ylu12358/mae-148-sp24-team4/CAD/GPS/GPS Antenna.SLDPRT

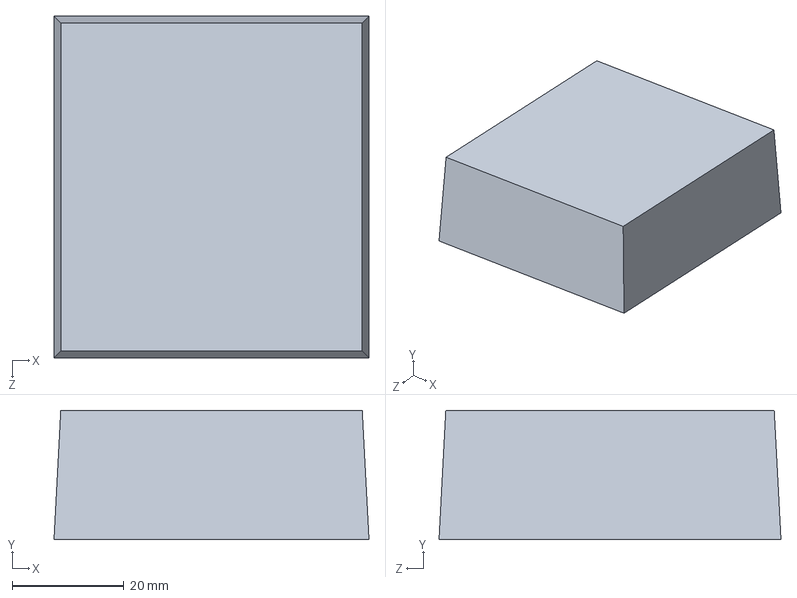
[picture p22: CAD file, 2024-04-26]
CAD/GPS/GPS Antenna.SLDPRT
56.5 x 23.1 x 61.3 mm
