ylu12358/mae-148-sp24-team4/CAD/Jetson/NanoMeshMini-Bottom-Jetson-Nano-DevKit-Case.stl

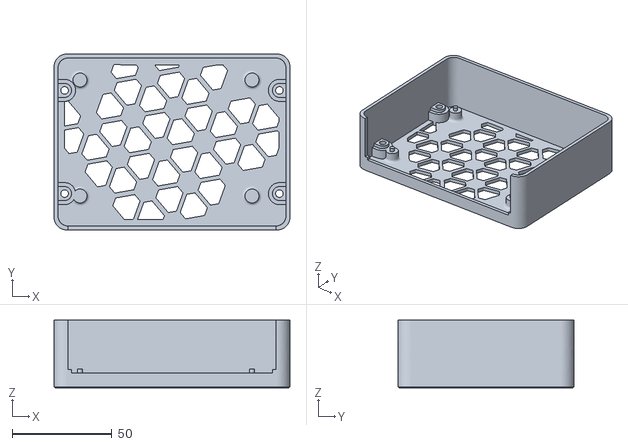
[picture p23: CAD file, 2024-04-19]
CAD/Jetson/NanoMeshMini-Bottom-Jetson-Nano-DevKit-Case.stl
118.0 x 88.0 x 34.0
