ylu12358/mae-148-sp24-team4/CAD/LIDAR/LIDAR Mount.SLDPRT

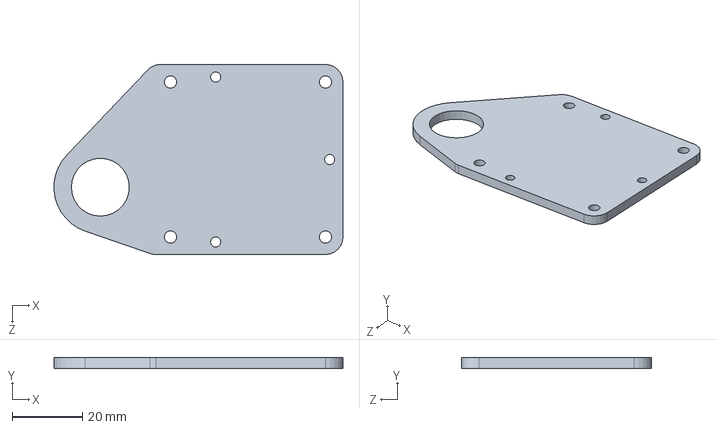
[picture p24: CAD file, 2024-04-28]
CAD/LIDAR/LIDAR Mount.SLDPRT
82.4 x 3.00 x 54.2 mm
