ylu12358/mae-148-sp24-team4/CAD/VESC.SLDPRT

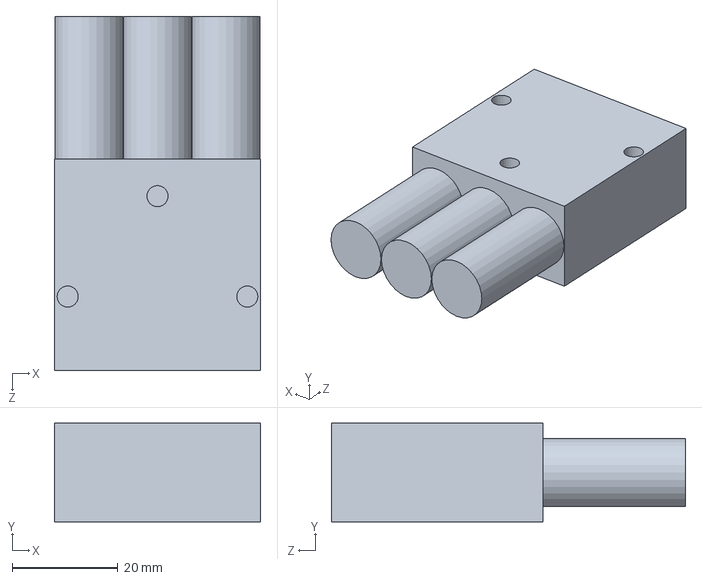
[picture p25: CAD file, 2024-04-19]
CAD/VESC.SLDPRT
39.0 x 18.7 x 67.0 mm
