ylu12358/mae-148-sp24-team4/CAD/Anti Spark Switch.SLDPRT

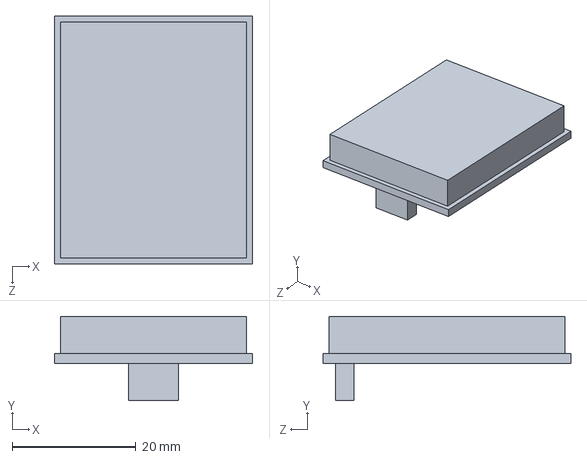
[picture p26: CAD file, 2024-04-19]
CAD/Anti Spark Switch.SLDPRT
32.0 x 13.6 x 40.0 mm
