ylu12358/mae-148-sp24-team4/CAD/Camera/Camera Mount Base.SLDPRT

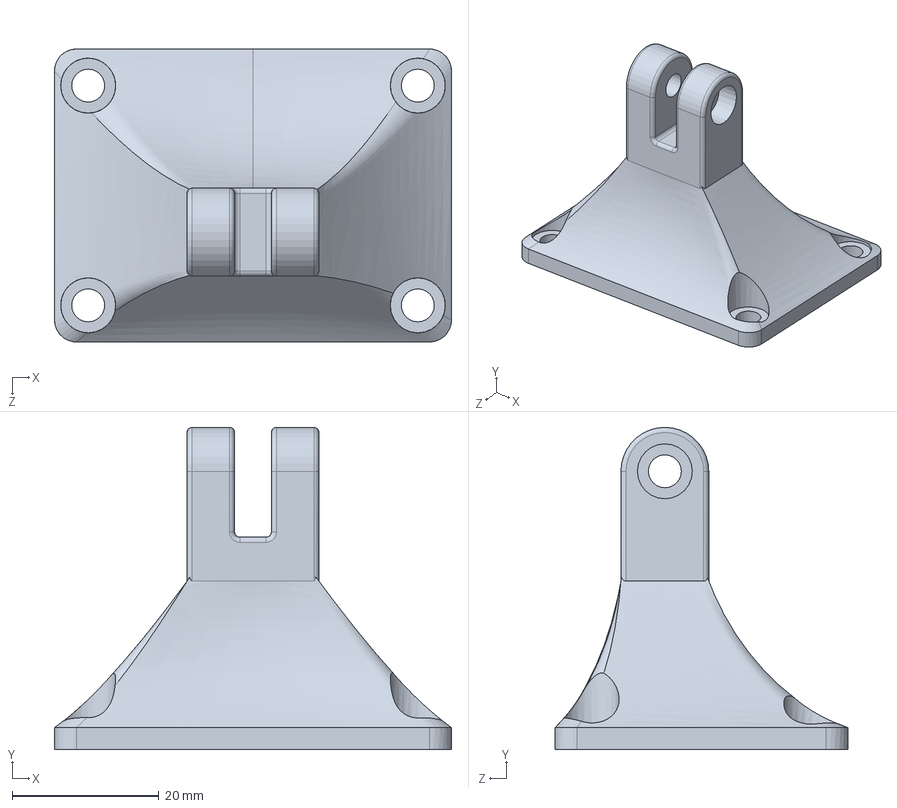
[picture p27: CAD file, 2024-04-19]
CAD/Camera/Camera Mount Base.SLDPRT
54.2 x 44.0 x 40.0 mm
