ylu12358/mae-148-sp24-team4/CAD/GPS/GPS.SLDPRT

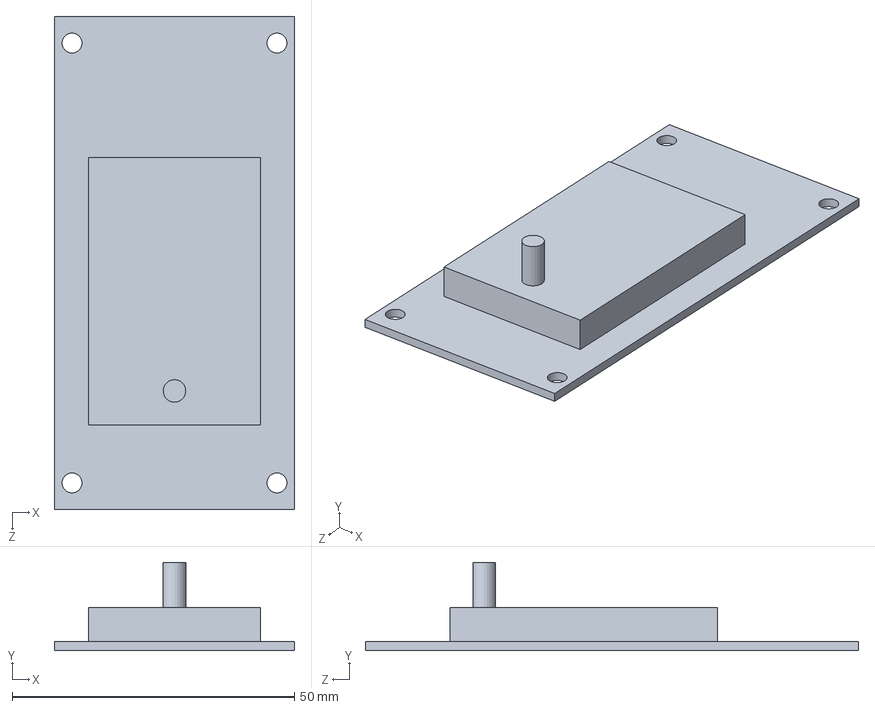
[picture p28: CAD file, 2024-04-26]
CAD/GPS/GPS.SLDPRT
42.5 x 15.6 x 87.3 mm
