ylu12358/mae-148-sp24-team4/CAD/Jetson/NanoMeshMini-Top-Jetson-Nano-DevKit-Case.stl

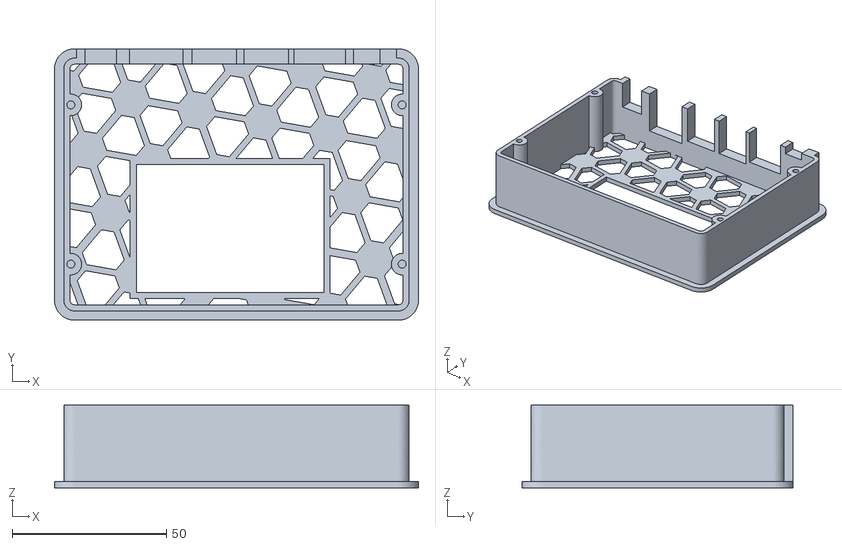
[picture p29: CAD file, 2024-04-19]
CAD/Jetson/NanoMeshMini-Top-Jetson-Nano-DevKit-Case.stl
118.0 x 88.0 x 26.8
