ylu12358/mae-148-sp24-team4/CAD/Battery.SLDPRT

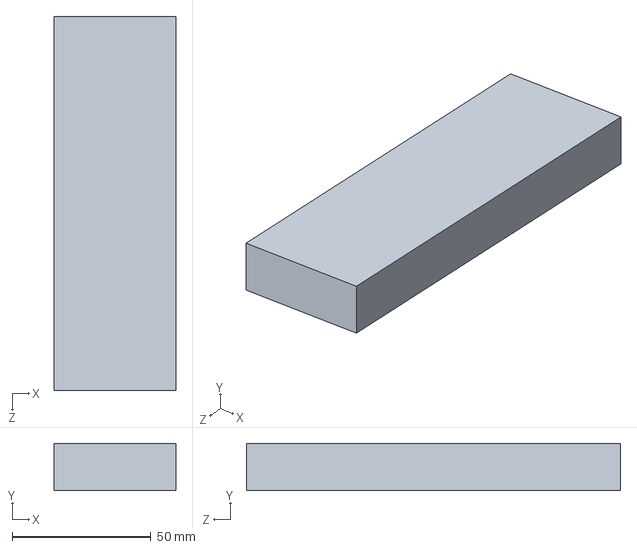
[picture p30: CAD file, 2024-04-19]
CAD/Battery.SLDPRT
44.0 x 17.0 x 135.0 mm
