ylu12358/mae-148-sp24-team4/CAD/Camera/Oak D Lite.SLDPRT

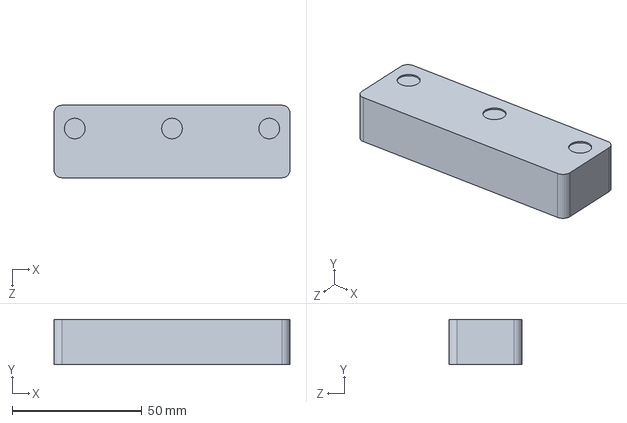
[picture p31: CAD file, 2024-04-19]
CAD/Camera/Oak D Lite.SLDPRT
91.0 x 17.5 x 28.0 mm
