ylu12358/mae-148-sp24-team4/CAD/USB Hub.SLDPRT

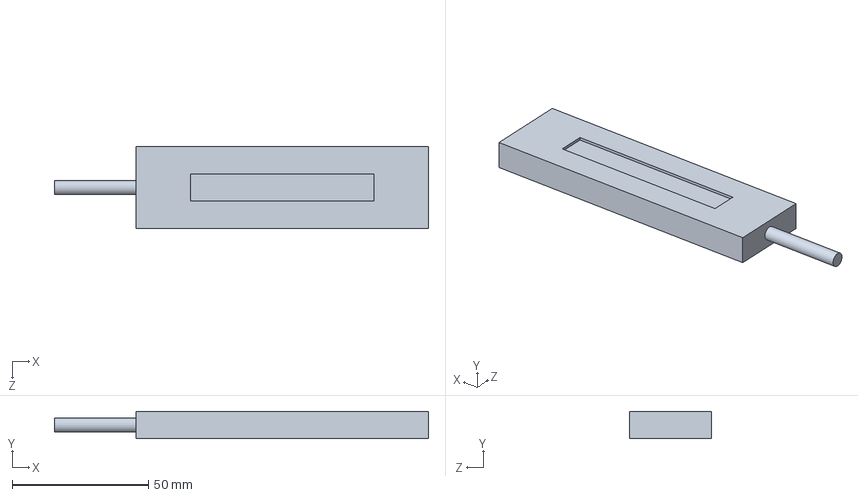
[picture p32: CAD file, 2024-04-19]
CAD/USB Hub.SLDPRT
137.3 x 10.0 x 30.0 mm
